spoonieau/Arsenic/Frimware/Arsenic-Firmware-WIFI/src/hychill30.cpp

/* 
Hychill30 digital pressure chart
Data pulled from https://hychill.com.au/media/pages/info/8815c50841-1662605920/hychill-pressure-temperature-chart-automotive.pdf
Will get temp in °C and match aganst kpa

Temp Range -10°C to 60°C

Written by rick spooner
 */

#include "hychill30.h"
#include "Arduino.h"

double hychill30::pressure (int temp)
{
    double x = 0.0;

    switch (temp)
    {
    case -10:
        x = 158.5;
        break;

    case -9:
        x = 168.9;
        break;

    case -8:
        x = 179.2;
        break;

    case -7:
        x = 189.6;
        break;

    case -6:
        x = 199.9;
        break;

    case -5:
        x = 206.8;
        break;

    case -4:
        x = 213.7;
        break;

    case -3:
        x = 224.0;
        break;

    case -2:
        x = 234.4;
        break;

    case -1:
        x = 248.2;
        break;

    case 0:
        x = 262.0;
        break;
    
    case 1:
        x = 272.3;
        break;

    case 2:
        x = 282.6;
        break;

    case 3:
        x = 293.0;
        break;

    case 4:
        x = 303.3;
        break;
    
    case 5:
        x = 317.1;
        break;
    
    case 6:
        x = 330.9;
        break;

    case 7:
        x = 344.7;
        break;

    case 8:
        x = 358.5;
        break;
    
    case 9:
        x = 372.3;
        break;
    
    case 10:
        x = 386.1;
        break;
    
    case 11:
        x = 399.8;
        break;

    case 12:
        x = 413.6;
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
    
    case 57:
        x = 1437.5;
        break;
    
    case 58:
        x = 1468.5;
        break;
    
    case 59:
        x = 1503.0;
        break;
    
    case 60:
        x = 1537.5;
        break;
    
    default:
        x = 0.0;
        break;
    }

    return x;
}
