spoonieau/Arsenic/Frimware/Arsenic-Firmware-WIFI/src/r1234yf.cpp

/* 
r1234yf digital pressure chart
Data pulled from Danfoss Cool Selector2 ver 5.1.0 'Refrigerant Calculator'
https://www.danfoss.com/en/service-and-support/downloads/dcs/coolselector-2/
Will get temp in °C and match aganst Kpa

Temp Range -10°C to 60°C

Written by rick spooner
 */
#include "r1234yf.h"
#include "Arduino.h"

double r1234yf::pressure (int temp)
{
    double x = 0.0;

    switch (temp)
    {
    case -10:
        x = 221.8;
        break;

    case -9:
        x = 230.1;
        break;

    case -8:
        x = 238.6;
        break;

    case -7:
        x = 247.4;
        break;

    case -6:
        x = 256.4;
        break;

    case -5:
        x = 265.6;
        break;

    case -4:
        x = 275.1;
        break;

    case -3:
        x = 284.9;
        break;

    case -2:
        x = 294.9;
        break;

    case -1:
        x = 305.2;
        break;

    case 0:
        x = 315.8;
        break;
    
    case 1:
        x = 326.7;
        break;

    case 2:
        x = 337.8;
        break;

    case 3:
        x = 349.2;
        break;

    case 4:
        x = 360.9;
        break;
    
    case 5:
        x = 372.9;
        break;
    
    case 6:
        x = 385.2;
        break;

    case 7:
        x = 397.8;
        break;

    case 8:
        x = 410.7;
        break;
    
    case 9:
        x = 424.0;
        break;
    
    case 10:
        x = 437.5;
        break;
    
    case 11:
        x = 451.4;
        break;

    case 12:
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
    
    case 57:
        x = 1534.0;
        break;
    
    case 58:
        x = 1569.0;
        break;
    
    case 59:
        x = 1605.0;
        break;
    
    case 60:
        x = 16.42;
        break;
    
    default:
        x = 0.0;
        break;
    }

    return x;
}
