spoonieau/Arsenic/Frimware/Arsenic-Firmware-WIFI/src/r134a.cpp

/* 
r134a digital pressure chart
Data pulled from Danfoss Cool Selector2 ver 5.1.0 'Refrigerant Calculator'
https://www.danfoss.com/en/service-and-support/downloads/dcs/coolselector-2/
Will get temp in °C and match aganst Kpa

Temp Range -10°C to 60°C

Written by rick spooner
 */
#include "r134a.h"
#include "Arduino.h"

double r134a::pressure (int temp)
{
    double x = 0.0;

    switch (temp)
    {
    case -10:
        x = 200.6;
        break;

    case -9:
        x = 208.7;
        break;

    case -8:
        x = 217.0;
        break;

    case -7:
        x = 225.5;
        break;

    case -6:
        x = 234.3;
        break;

    case -5:
        x = 243.4;
        break;

    case -4:
        x = 252.7;
        break;

    case -3:
        x = 262.3;
        break;

    case -2:
        x = 272.2;
        break;

    case -1:
        x = 282.4;
        break;

    case 0:
        x = 292.9;
        break;
    
    case 1:
        x =303.6;
        break;

    case 2:
        x = 314.7;
        break;

    case 3:
        x = 326.1;
        break;

    case 4:
        x = 337.8;
        break;
    
    case 5:
        x = 349.8;
        break;
    
    case 6:
        x = 362.1;
        break;

    case 7:
        x = 374.7;
        break;

    case 8:
        x = 387.7;
        break;
    
    case 9:
        x = 401.0;
        break;
    
    case 10:
        x = 414.7;
        break;
    
    case 11:
        x = 428.7;
        break;

    case 12:
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
    
    case 57:
        x = 1565.0;
        break;
    
    case 58:
        x = 1603.0;
        break;
    
    case 59:
        x = 1642.0;
        break;
    
    case 60:
        x = 1681.0;
        break;
    
    default:
        x = 0.0;
        break;
    }

    return x;
}
